WillemViljoen22877169/E448/Latex/frontmatter/skripsie_title_page.tex

\graphicspath{{frontmatter/fig/}}
\pagenumbering{Alph}

\begin{titlepage}
\begin{center}



\vfill

		{\sffamily \bfseries \huge a Modular Battery Management System for LFP Batteries \par}
		
		\vspace{7em}
		
		{\large {\Large  Willem Viljoen} \\ 22877169 \par}

		\vspace{8em}
		
		{Report presented in partial fulfilment of the requirements for the degree of Electrical Engineering in the Faculty of Engineering at Stellenbosch University. \par}
		
		\vfill
  
        {\large {Supervisor}: Dr JM\ Strauss \par}		
		{Department of Electrical and Electronic Engineering \par}

\vfill

%{\large {Supervisor}: Dr L. Skywalker} %\\
% Department of Electrical and Electronic Engineering \par}

\vfill

{\Large \myDate}
\end{center}
\end{titlepage}
