WillemViljoen22877169/E448/Admin/Meeting Notes/Comms_Idea.pdf

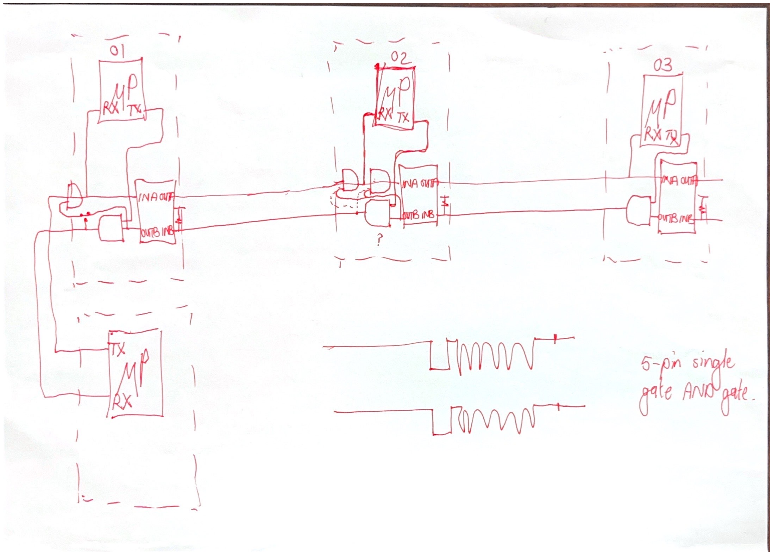
[picture p46: page 1]
