WillemViljoen22877169/E448/Admin/Meeting Notes/Main_Idea.pdf

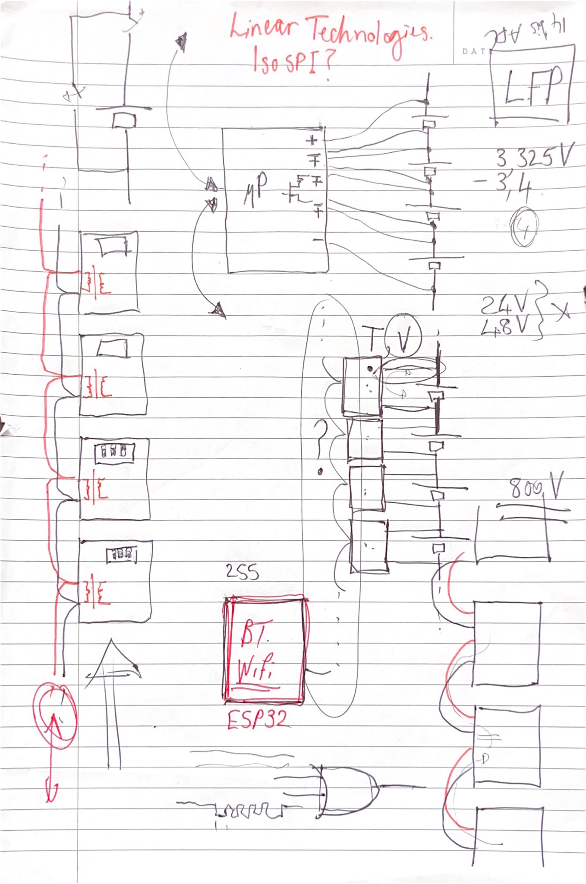
[picture p47: page 1]
