WillemViljoen22877169/E448/Admin/Meeting Notes/Skripsie_Ideas.pdf

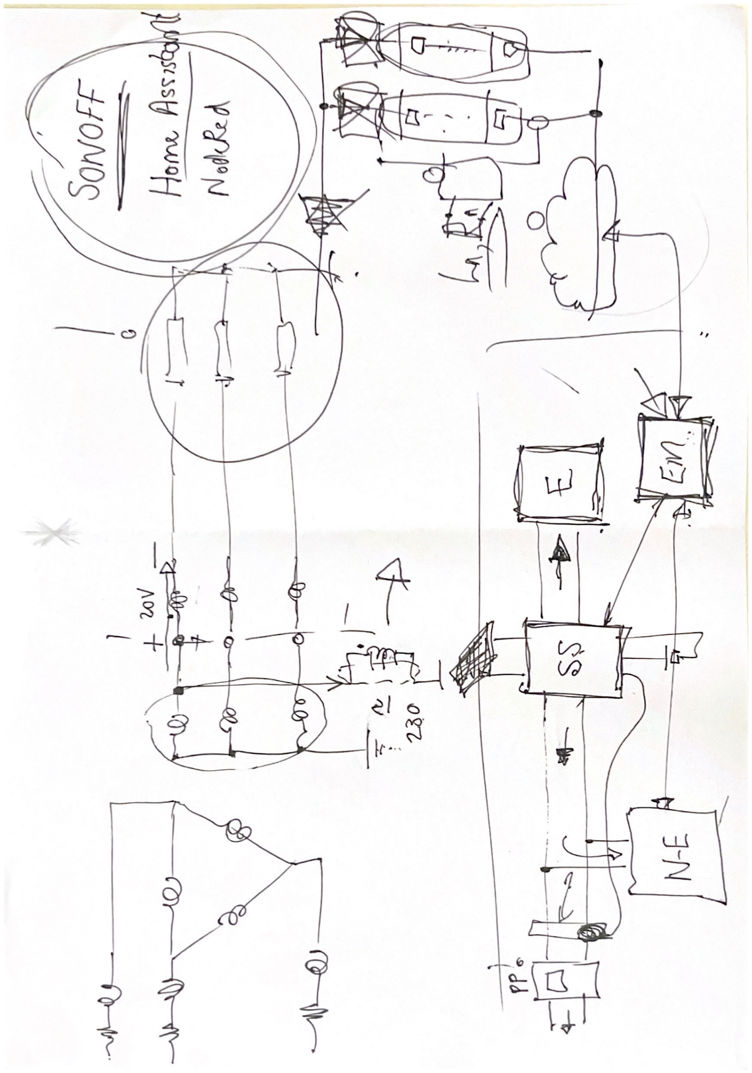
[picture p48: page 1]
