WillemViljoen22877169/E448/Admin/info.png

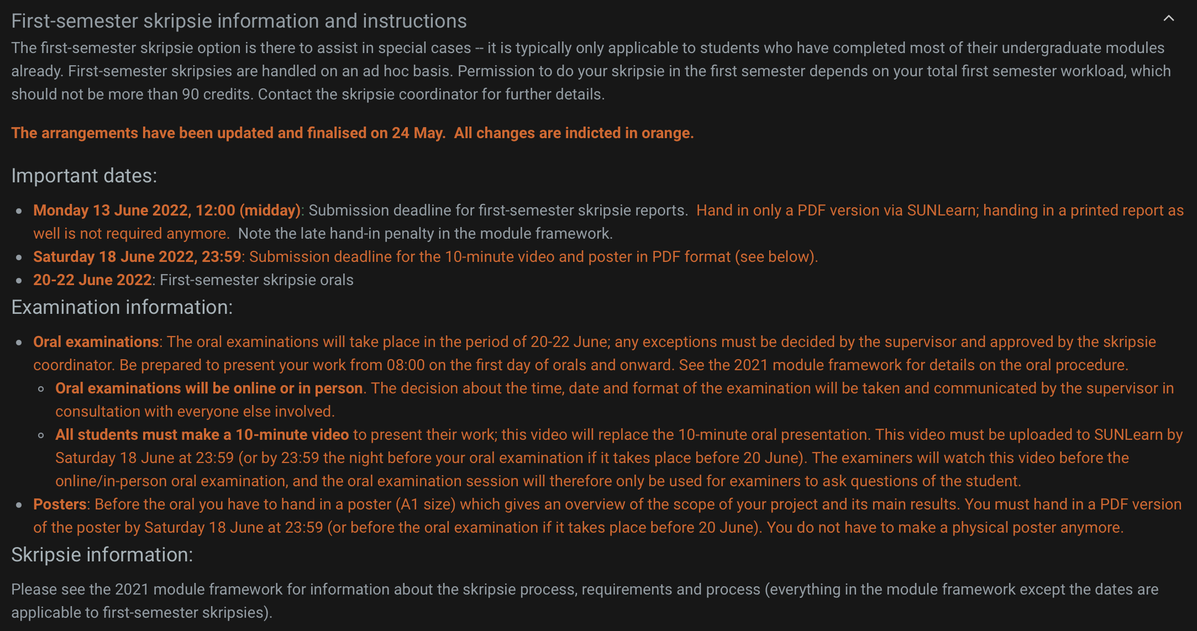
Admin/info.png
