WillemViljoen22877169/E448/Latex/Figures/commsBlockDia.png

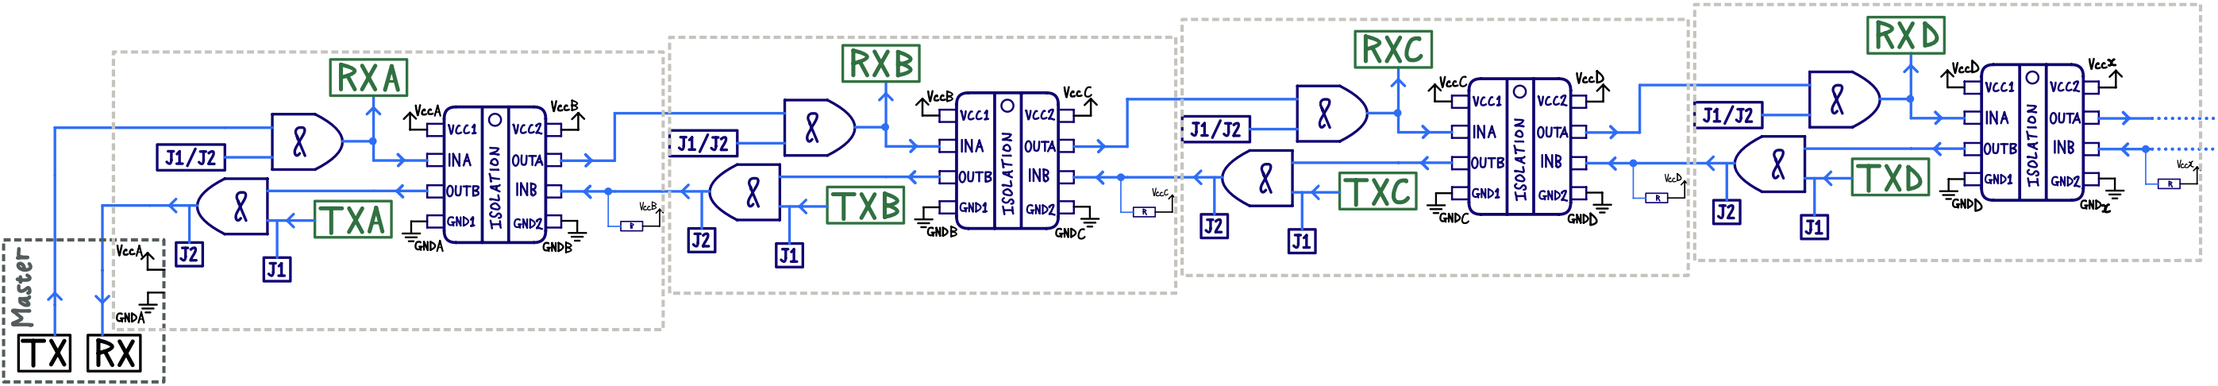
Latex/Figures/commsBlockDia.png
