WillemViljoen22877169/E448/Latex/Figures/Placeholder.png

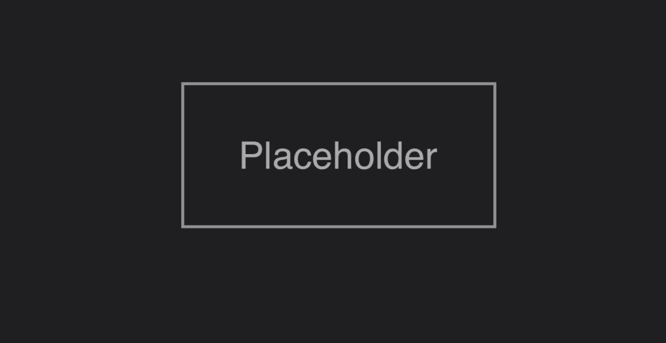
Latex/Figures/Placeholder.png
