WillemViljoen22877169/E448/Latex/frontmatter/fig/Signature.png

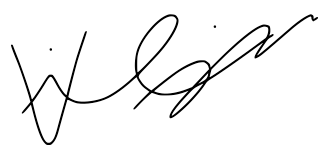
Latex/frontmatter/fig/Signature.png
