WillemViljoen22877169/E448/Admin/Orders/Components.png

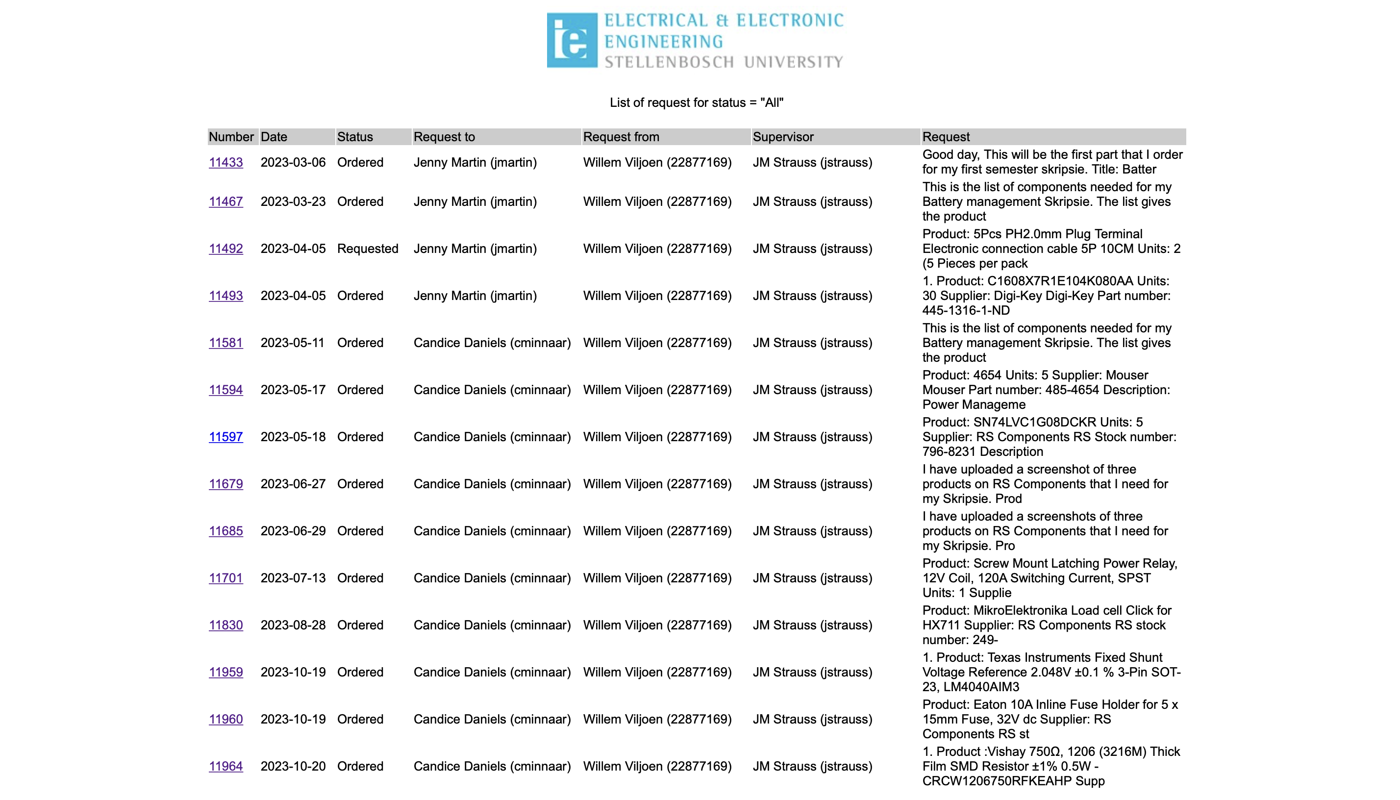
Admin/Orders/Components.png
