WillemViljoen22877169/E448/Tests/Pulsed_Discharge/BMS_Model.png

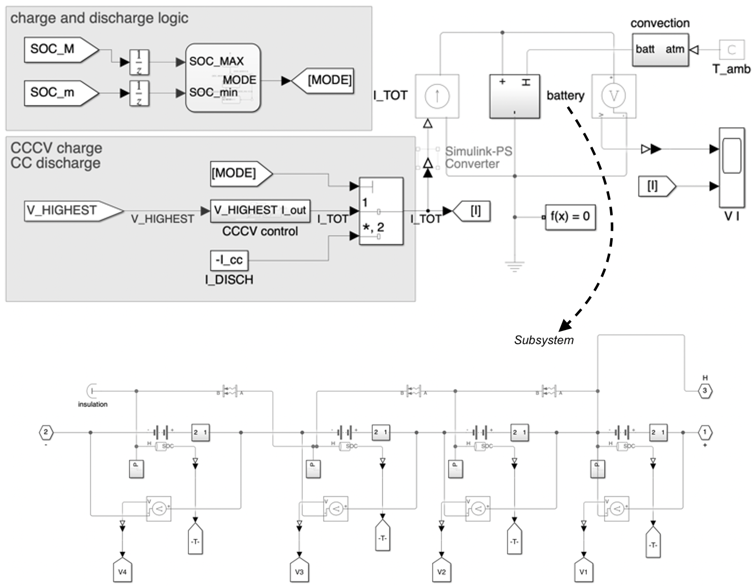
Tests/Pulsed_Discharge/BMS_Model.png
