WillemViljoen22877169/E448/Tests/Pulsed_Discharge/ParamEst_Model.png

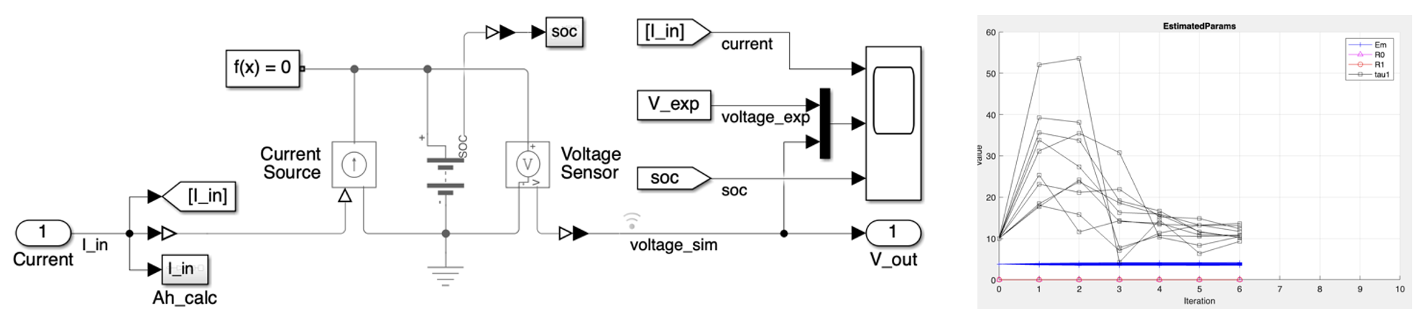
Tests/Pulsed_Discharge/ParamEst_Model.png
