WillemViljoen22877169/E448/Tests/Pulsed_Discharge/Sim_Results/I_V_Cells.png

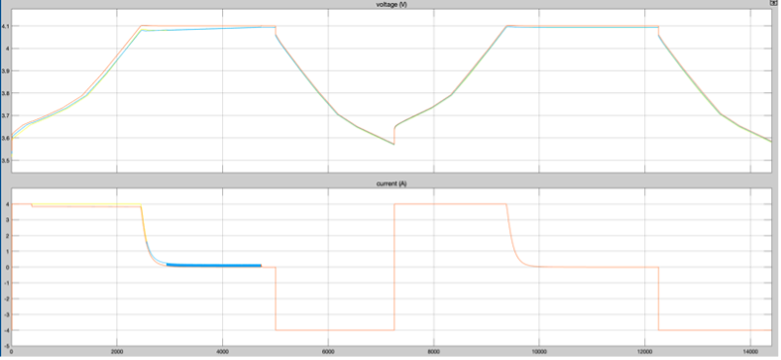
Tests/Pulsed_Discharge/Sim_Results/I_V_Cells.png
