WillemViljoen22877169/E448/Tests/Pulsed_Discharge/Sim_Results/T_Cells.png

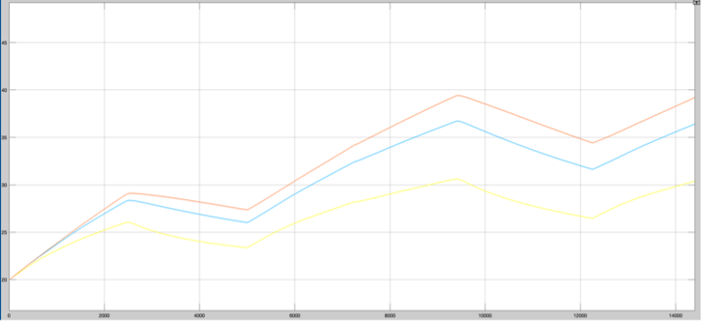
Tests/Pulsed_Discharge/Sim_Results/T_Cells.png
