WillemViljoen22877169/E448/Tests/Thermal_100A/Thermal_Camera.png

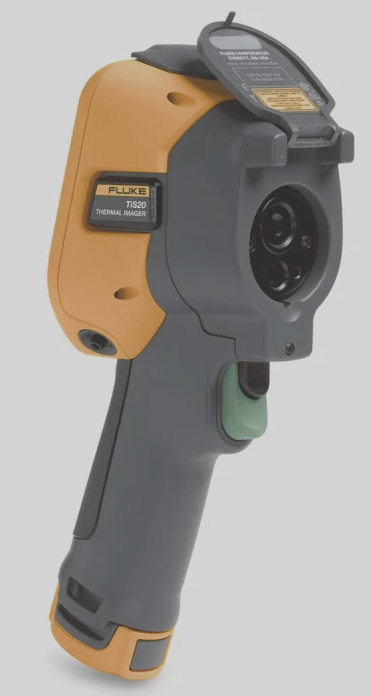
Tests/Thermal_100A/Thermal_Camera.png
