WillemViljoen22877169/E448/KiCad/Mstr_Controller_Board_v01/Drawing.pdf

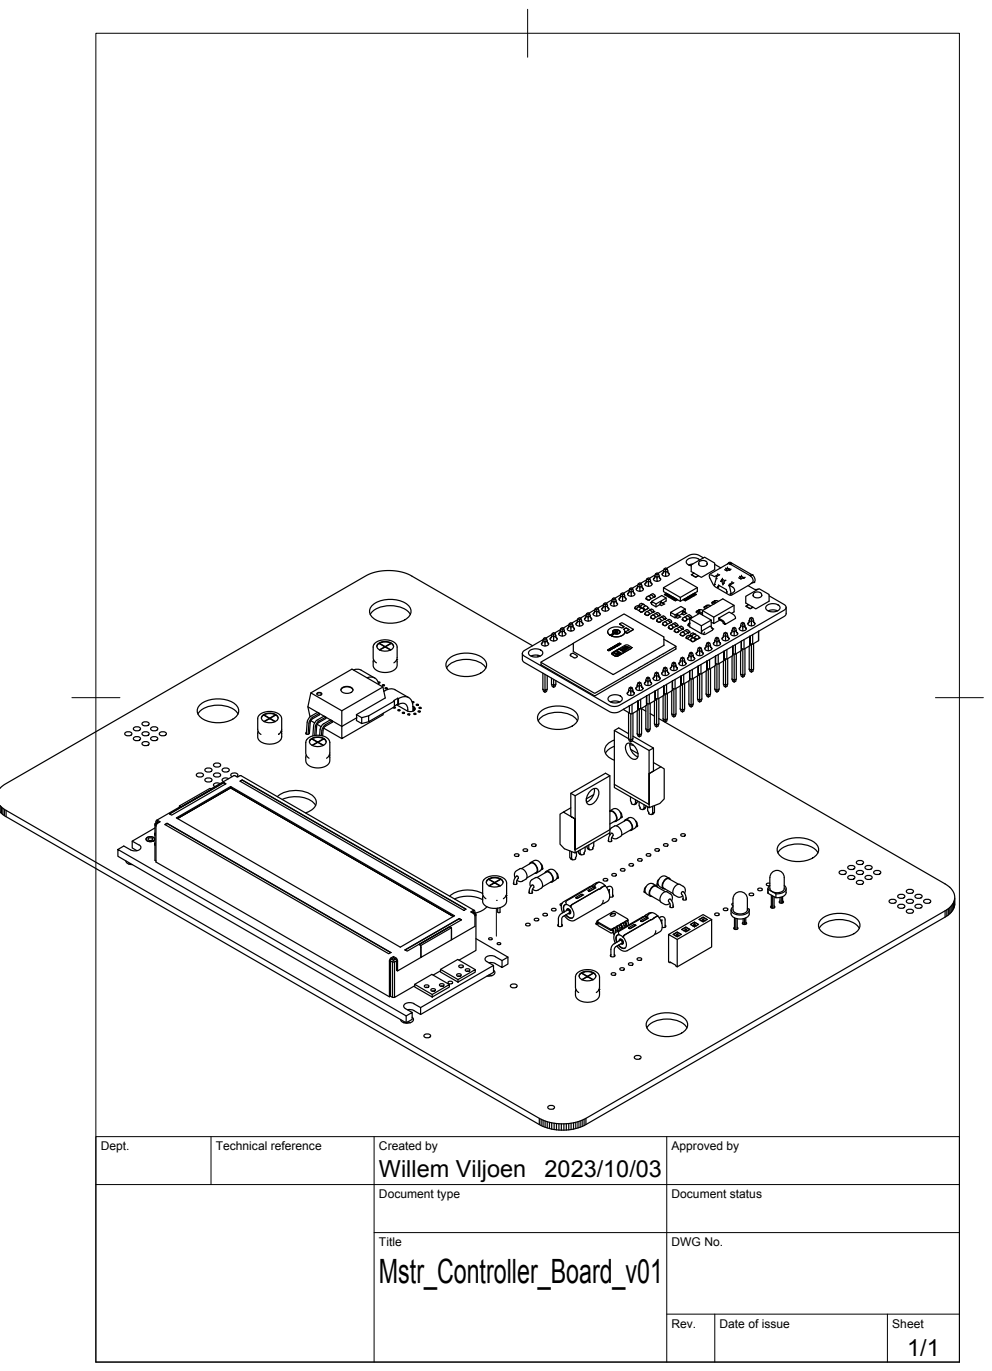
[picture p65: page 1]

Dept. | Technical reference | Created by Willem Viljoen 2023/10/03 | Approved by

Document type | Document status

Title Mstr_Controller_Board_v01 | DWG No.

Rev. | Date of issue | Sheet 1/1
