WillemViljoen22877169/E448/KiCad/Mstr_Controller_Board_v01/PCB.pdf

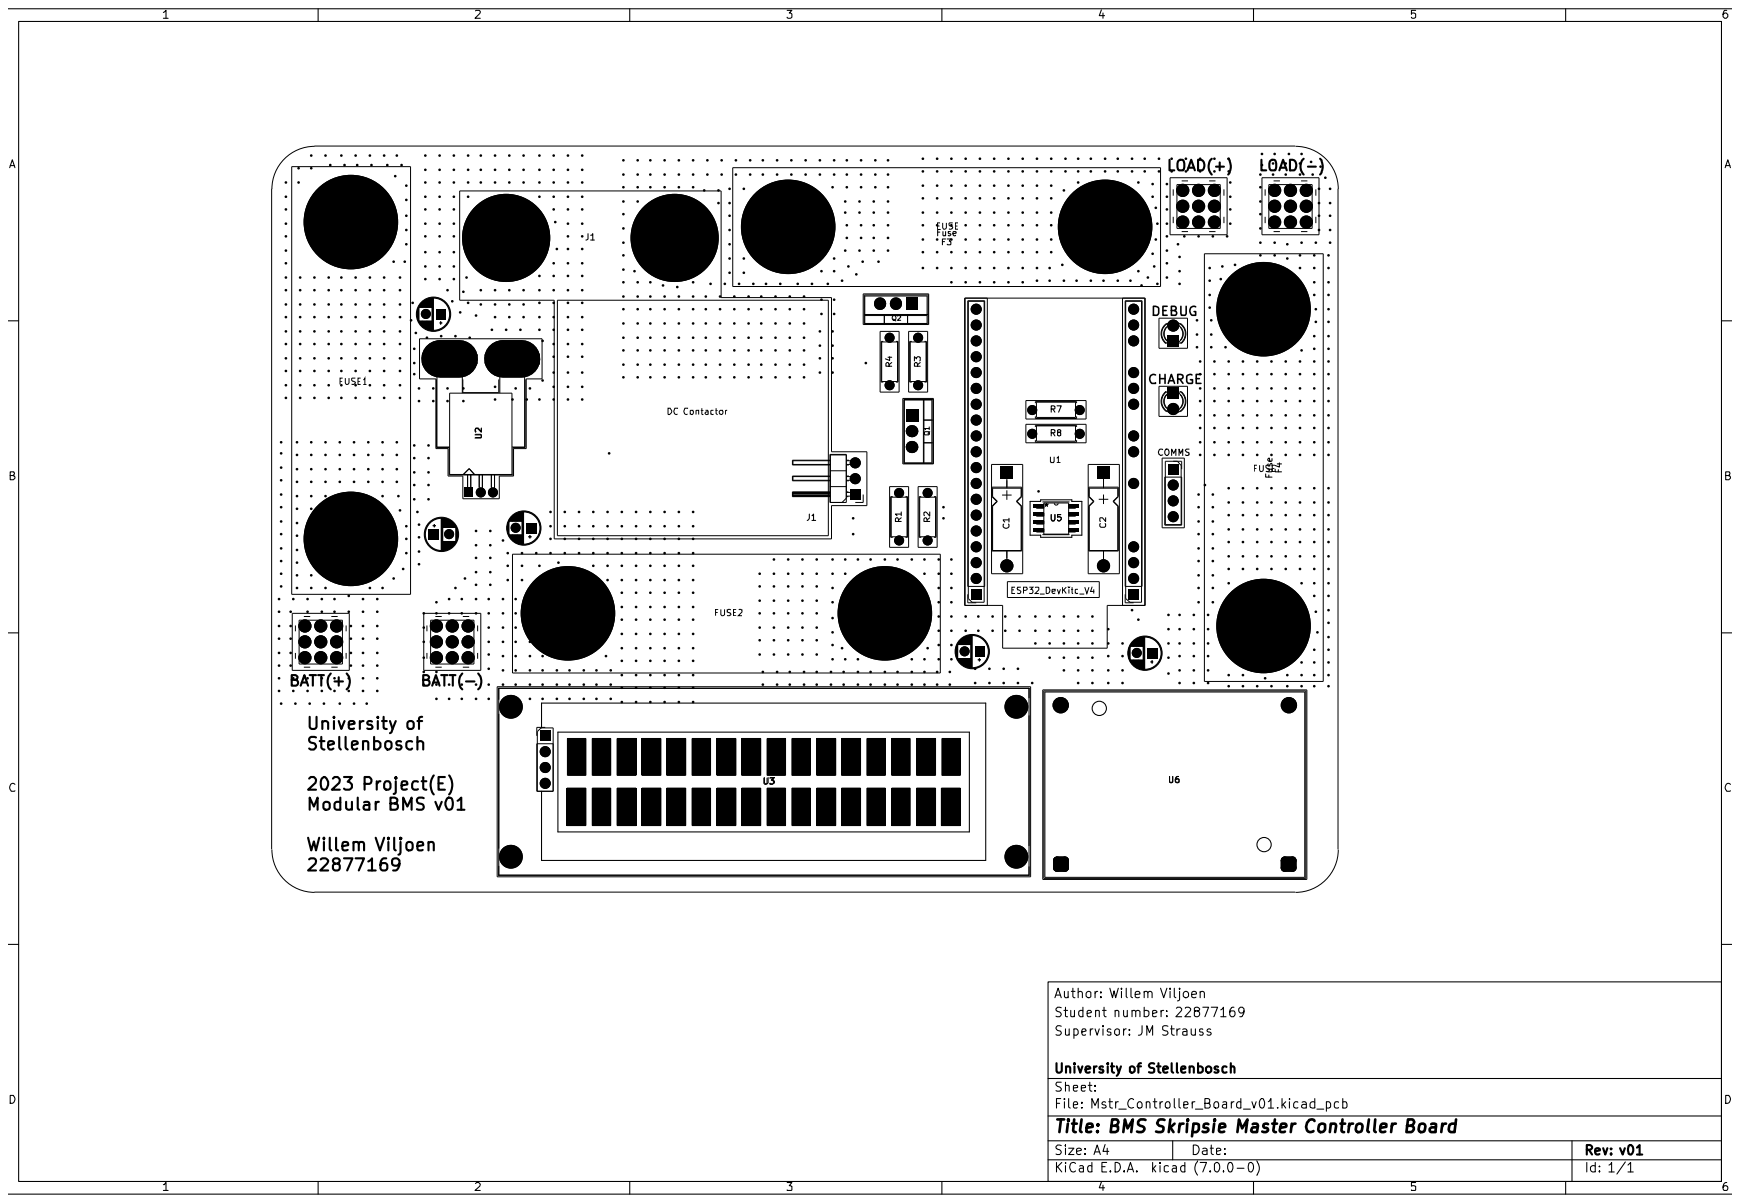
[picture p66: page 1]
