WillemViljoen22877169/E448/KiCad/Monitoring_Board_v01/Drawing.pdf

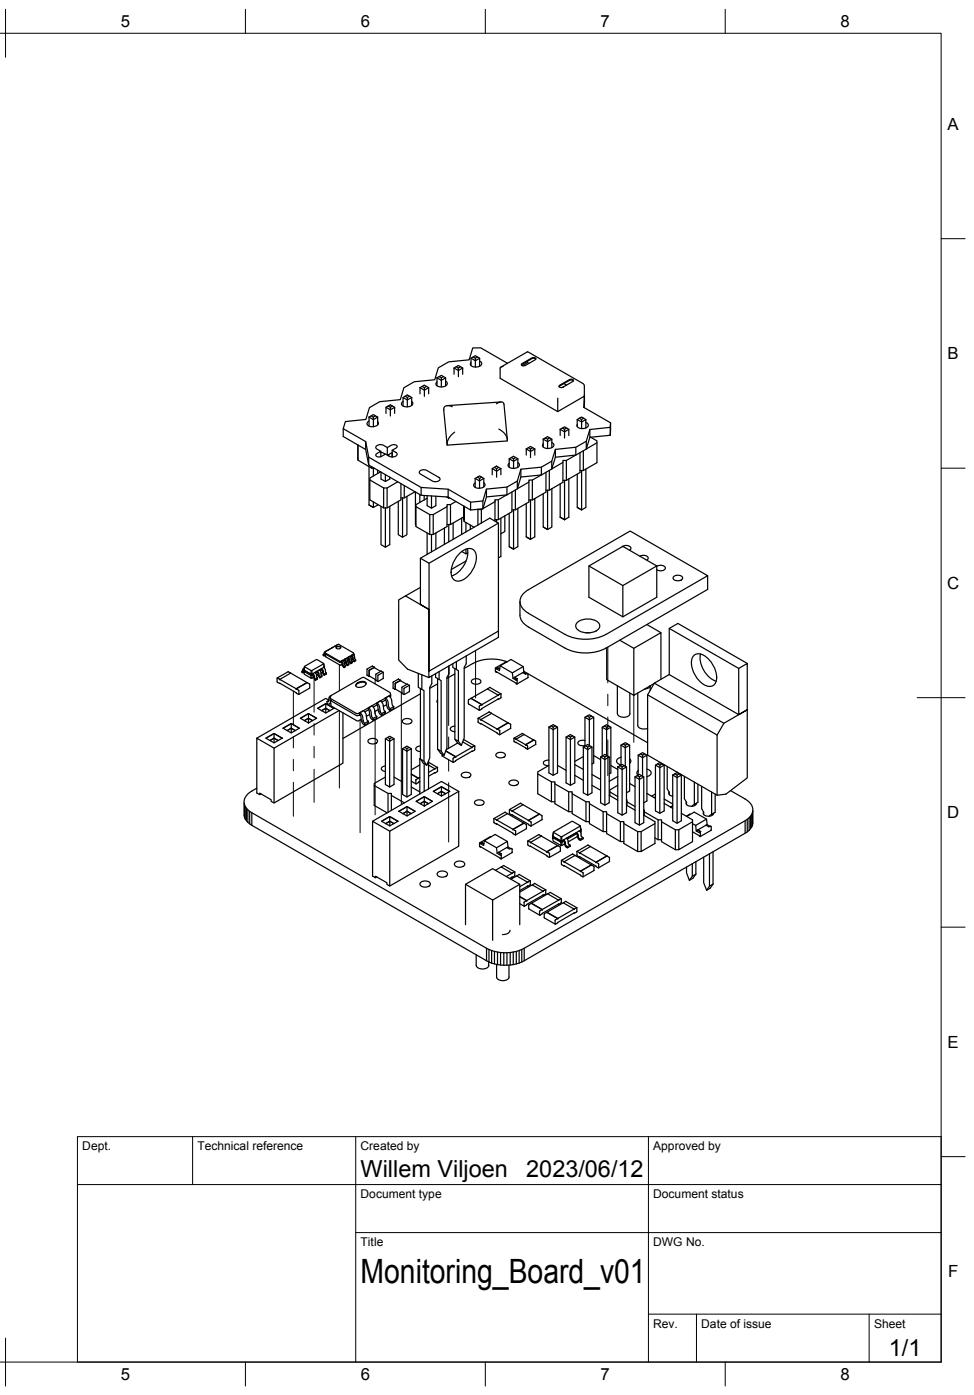
[picture p67: page 1]
8 BCDEF; ABCDEF

Dept. | Technical reference | Created by Willem Viljoen 2023/06/12 | Approved by

Document type | Document status

Title Monitoring_Board_v01 | DWG No.

Rev. | Date of issue | Sheet 1/1
