WillemViljoen22877169/E448/KiCad/Monitoring_Board_v01/PCB.pdf

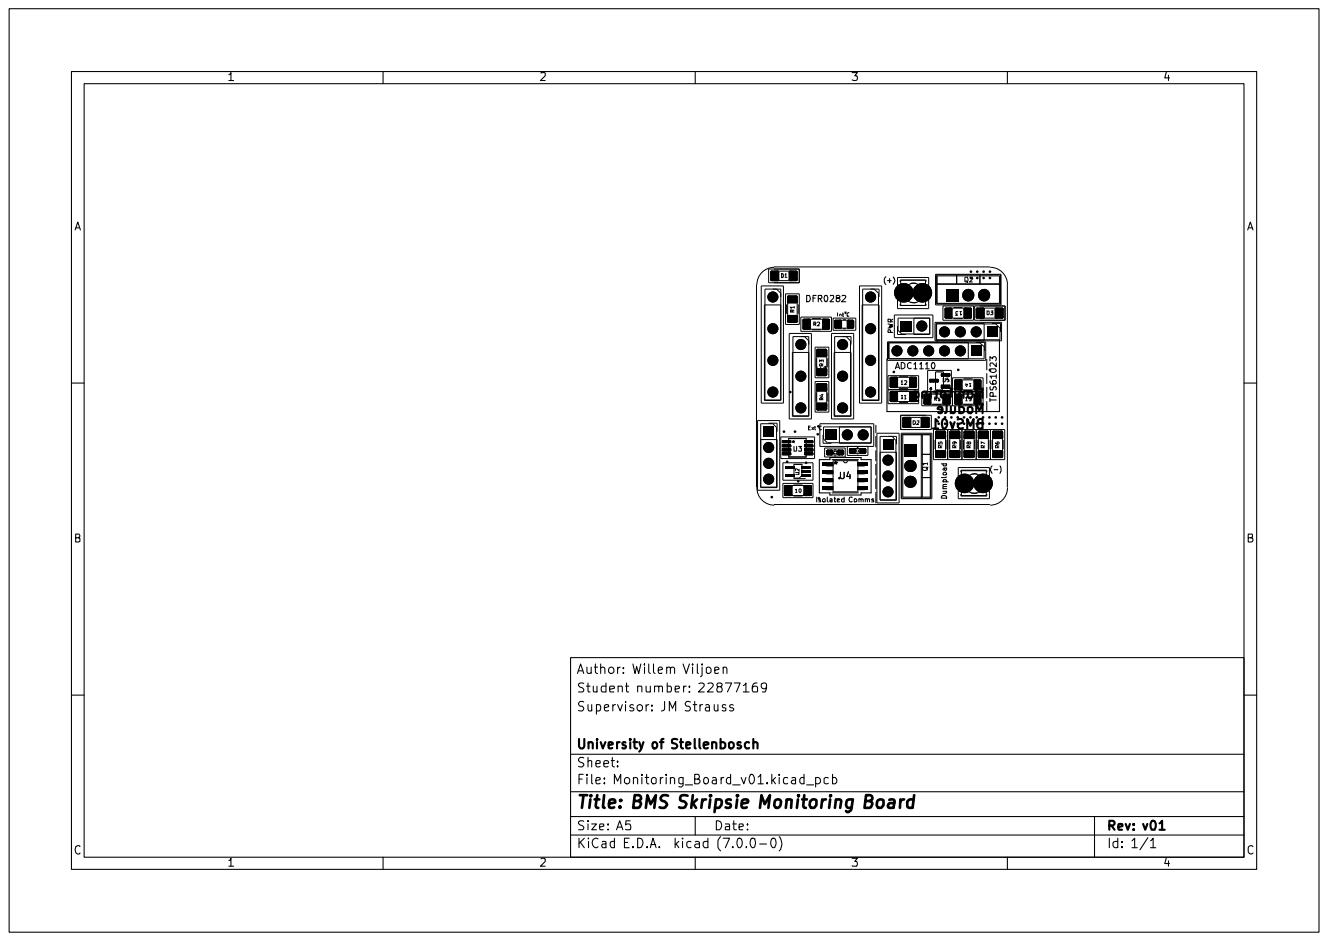
[picture p68: page 1]
